Prokuon/CardputerADV_Cap_TFT_V2/assets/20260829213334.jpg

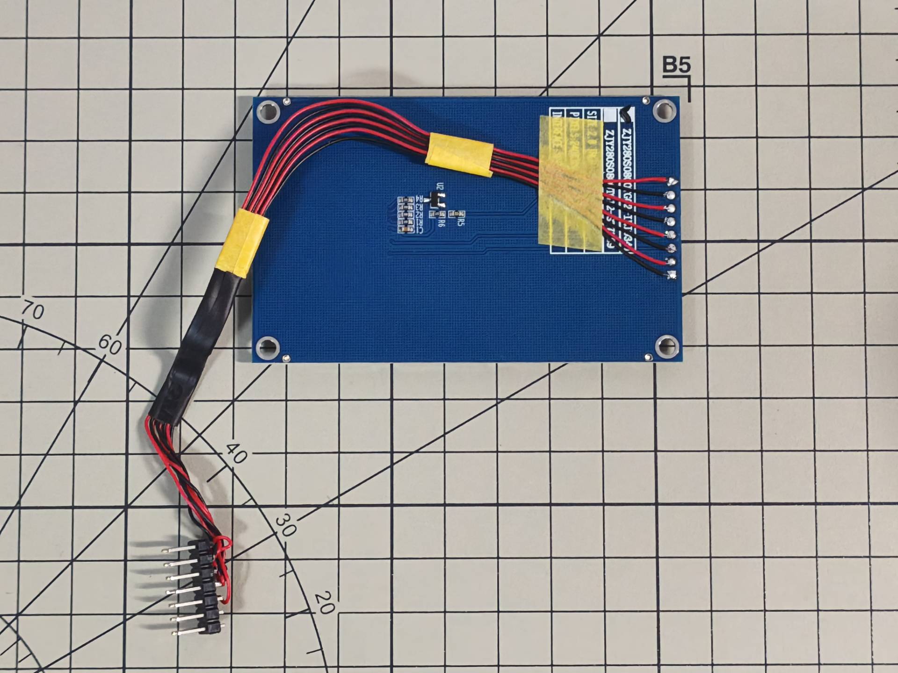
assets/20260829213334.jpg
