Prokuon/CardputerADV_Cap_TFT_V2/assets/20260829225138.jpg

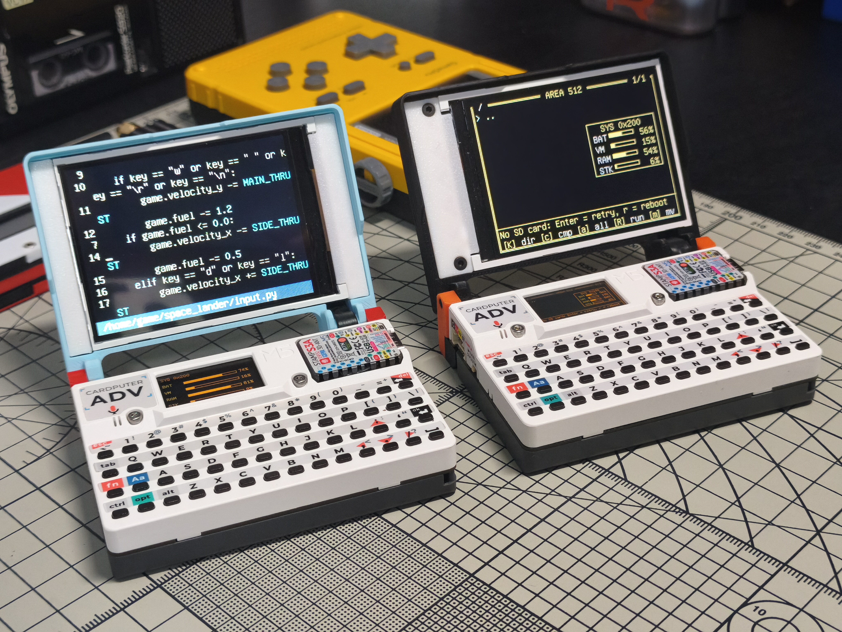
assets/20260829225138.jpg
